P-Shreyas543/ACIR-Learning-Kit-1-PCB/ACIR-Learning-Kit-1-PCB/kit1_render_isometric.png

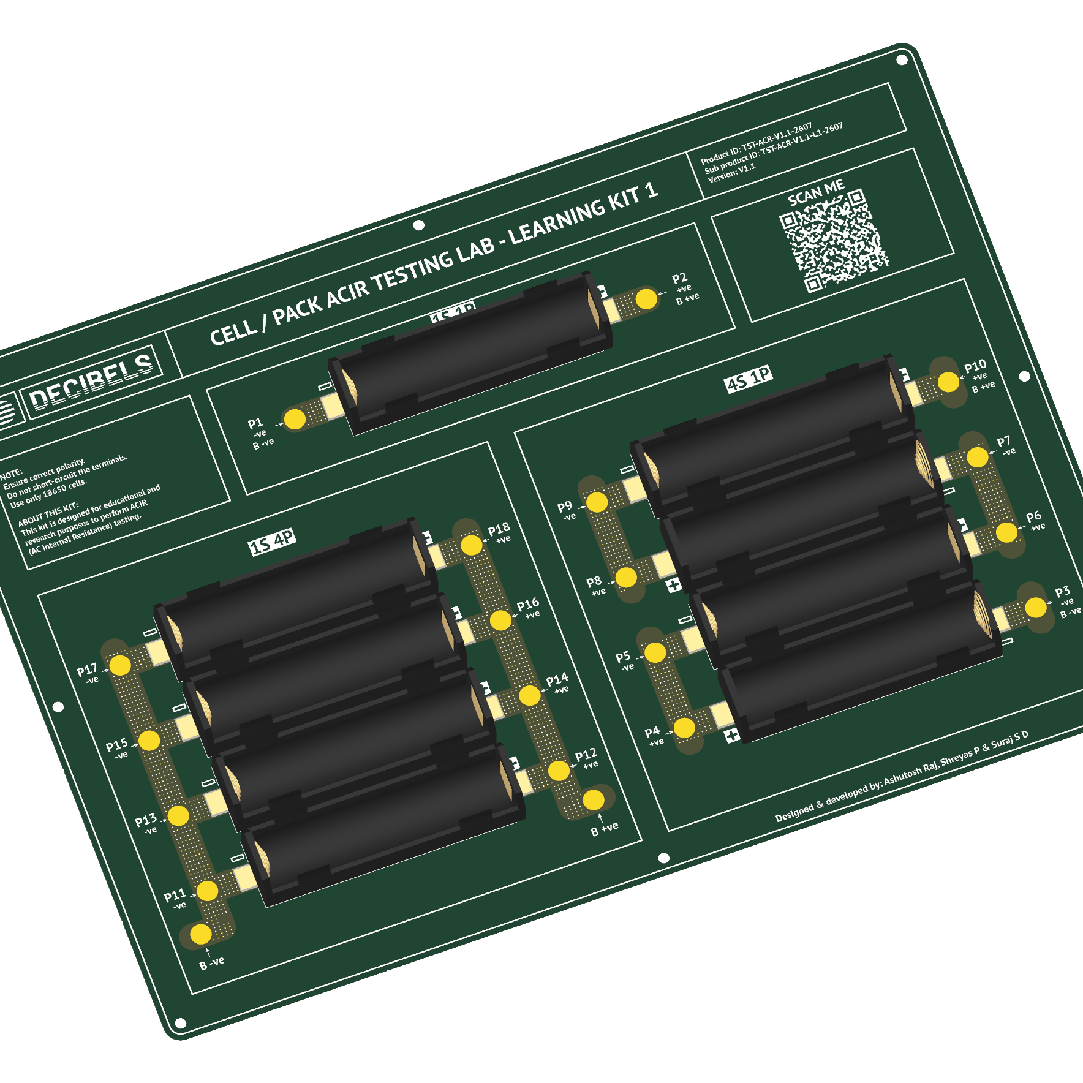
ACIR-Learning-Kit-1-PCB/kit1_render_isometric.png
